kevinlutzer/strato-connect/code/strato-connect/AX25_test.h

#include <gtest/gtest.h>
#include <iostream>
#include "AX25.h"

namespace {
  // Tests the default c'tor.
  TEST(AX25, applyCallsign) {
    AX25 ax25;
    
    // allocate frame to just contain the callsign
    uint8_t *frame = (uint8_t*)calloc(14, sizeof(uint8_t));
    if (frame == NULL) {
      FAIL();
    }

    // Apply regular callsign with 6 alpha numerica characters with an ssid of 0
    char *callsign = "V3WA52"; // random callsign
    uint8_t ssid = 0x01;
    ax25.applyCallsign(frame, 0, callsign, ssid);

    // Make sure we add 
    for (int i = 0; i < 6; i++) {
      EXPECT_EQ(frame[i], (uint8_t)callsign[i]);
    }
    EXPECT_EQ(frame[6], ssid);

    callsign = "bec---";
    ssid = 0xFF;
    ax25.applyCallsign(frame, 7, callsign, ssid);

    // Make sure we add 
    for (int i = 7; i < 13; i++) {
      EXPECT_EQ(frame[i], (uint8_t)callsign[i]);
    }
    EXPECT_EQ(frame[13], ssid);
  }
}  // namespace
